going-digital/one-rom/sdrr/src/rp235x.c

// One ROM RP235X Specific Routines

// Copyright (C) 2026 Piers Finlayson <piers@piers.rocks>
//
// MIT License

#define RP235X_INCLUDES
#include "include.h"

#if defined(RP235X)

#include "roms.h"

#if defined(RP2350A) && defined(RP2350B)
#error "Cannot define both RP2350A and RP2350B"
#elif !defined(RP2350A) && !defined(RP2350B)
#error "Must define either RP2350A or RP2350B" 
#endif // RP2350A && RP2350B

// Internal function prototypes
uint8_t calculate_pll_settings(
    rp235x_clock_config_t *clock_config,
    uint8_t overclock
);
void get_clock_config(rp235x_clock_config_t *config);
uint8_t get_vreg_from_target_mhz(uint16_t target_mhz);
void setup_xosc(void);
void setup_pll(rp235x_clock_config_t *config);
void setup_usb_pll(void);
void setup_qmi(rp235x_clock_config_t *config);
void setup_vreg(rp235x_clock_config_t *config);
void setup_adc(void);
void setup_cp(void);
void final_checks(rp235x_clock_config_t *config);
uint16_t get_temp(void);

// RP2350 firmware needs a special boot block so the bootloader will load it.
// See datasheet S5.9.5 and ../include/reg-rp235x.h.
// It must be in the first 4KB of the flash firmware image.  This follows our
// reset vectors, which is fine.  Given we do not include a VECTOR_TABLE
// block, the bootloader assumes it is present at the start of flash - which it
// is.
#if !defined(TEST_BUILD)
__attribute__((section(".rp2350_block")))
#endif // !TEST_BUILD
const rp2350_boot_block_t rp2350_arm_boot_block = {
    .start_marker    = 0xffffded3,
    .image_type_tag  = 0x42,
    .image_type_len  = 0x1,
    .image_type_data = 0b0001000000100001,
    .type            = 0xff,
    .size            = 0x0001,
    .pad             = 0,
    .next_block      = 0,
    .end_marker      = 0xab123579
};

#if !defined(TEST_BUILD)

void platform_specific_init(void) {
    // RP235X needs to reset the JTAG interface to enable SWD (for example for
    // RTT logging)
    RESET_RESET |= RESET_JTAG;
    RESET_RESET &= ~RESET_JTAG;
    while (!(RESET_DONE & RESET_JTAG));
    DEBUG("JTAG reset complete");
}

// Set up interrupt to fire when VBUS sensed on PA9
void setup_vbus_interrupt(void) {
    // Check we have the information required to enable DFU
    if ((sdrr_info.extra->usb_port != PORT_0) ||
        (sdrr_info.extra->vbus_pin >= MAX_USED_GPIOS)) {
        ERR("Invalid USB port or pin for VBUS detect - not enabling USB DFU");
        return;
    }
    uint8_t vbus_pin = sdrr_info.extra->vbus_pin;

    // Enable VBUS detect interrupt
    GPIO_CTRL(vbus_pin) = GPIO_CTRL_RESET;      // Enable SIO
    uint32_t reg_offset = vbus_pin / 8;         // Which INTEx register (0-3)
    uint32_t bit = ((vbus_pin % 8) * 4) + 3;    // Bit within that register
    volatile uint32_t *inte = &IO_BANK0_PROC0_INTE0 + reg_offset;
    volatile uint32_t *intr = &IO_BANK0_INTR0 + reg_offset;
    *inte |= (1 << bit);                        // Enable rising edge interrupt
    *intr = (1 << bit);                         // Clear any pending
    NVIC_ISER0 |= (1 << IO_IRQ_BANK0);          // Enable IO_BANK0 interrupt in NVIC

    // Set as input, pull-down, output disable
    GPIO_PAD(vbus_pin) |= (PAD_PD | PAD_OUTPUT_DISABLE | PAD_INPUT);

    // Wait for pull-down to settle.  Using same delay as STM32 implementation.
    for (volatile int ii = 0; ii < 1000; ii++);

    // Check if VBUS already present
    if (GPIO_READ(vbus_pin)) {
        LOG("VBUS already present - entering bootloader");
        for (volatile int ii = 0; ii < 1000000; ii++);
        enter_bootloader();
    }
}

// VBUS interrupt Handler
void vbus_connect_handler(void) {
    // Clear the interrupt
    uint8_t vbus_pin = sdrr_info.extra->vbus_pin;
    uint32_t reg_offset = vbus_pin / 8;
    uint32_t bit = ((vbus_pin % 8) * 4) + 3;
    volatile uint32_t *intr = &IO_BANK0_INTR0 + reg_offset;
    *intr = (1 << bit);

    // Disable interrupts before logging
    __asm volatile("cpsid i");

        // Log and pause for log to complete
    LOG("VBUS detected - entering bootloader");
    for (volatile int ii = 0; ii < 1000000; ii++);

    enter_bootloader();
}
#endif // !TEST_BUILD

uint8_t calculate_pll_settings(
    rp235x_clock_config_t *config,
    uint8_t overclock
) {
    const uint32_t XOSC_MHZ = 12;
    const uint8_t REFDIV = 1;

    (void)overclock;
    
    uint32_t target_freq_mhz = config->sys_clock_freq_mhz;

    if ((target_freq_mhz > RP235X_STOCK_CLOCK_SPEED_MHZ) && (!overclock)) {
        ERR("Requested frequency %dMHz exceeds max %dMHz - cannot calculate PLL",
            target_freq_mhz, RP235X_STOCK_CLOCK_SPEED_MHZ);
        return 0;
    }
    
    uint32_t vco_min = 750;
    uint32_t vco_max = 1600;
    
    // Try POSTDIV combinations (prefer higher PD1:PD2 ratios)
    uint32_t best_error = UINT32_MAX;
    uint8_t rc = 0;
    for (uint8_t pd2 = 1; pd2 <= 7; pd2++) {
        for (uint8_t pd1 = 1; pd1 <= 7; pd1++) {
            uint32_t divisor = pd1 * pd2;
            uint32_t vco_mhz = target_freq_mhz * divisor;
            
            uint32_t fbdiv = (vco_mhz + 6) / XOSC_MHZ;  // Round to nearest
            
            if (fbdiv >= 16 && fbdiv <= 320) {
                uint32_t actual_vco = XOSC_MHZ * fbdiv;
                if (actual_vco >= vco_min && actual_vco <= vco_max) {
                    uint32_t target_vco = target_freq_mhz * divisor;
                    uint32_t error = (actual_vco > target_vco) ? 
                                    (actual_vco - target_vco) : 
                                    (target_vco - actual_vco);
                                    
                    if (error < best_error) {
                        best_error = error;
                        config->pll_refdiv = REFDIV;
                        config->pll_sys_fbdiv = (uint16_t)fbdiv;
                        config->pll_sys_postdiv1 = pd1;
                        config->pll_sys_postdiv2 = pd2;
                        rc = 1;
                    }
                }
            }
        }
    }
    
    return rc;
}

uint8_t get_vreg_from_target_mhz(uint16_t target_mhz) {
    uint8_t vreg = FIRE_VREG_1_10V;
    
    // These are conservative values.  The RP235X accepts values up to 3.30V.
    // Higher values may be required for very high overclocks, but may also
    // damage the chip or reduce its lifespan.
    //
    // To use custom VREG settngs, use firmware overrides in the ROM config.
    if (target_mhz >= 500) {
        vreg = FIRE_VREG_1_60V;
    } else if (target_mhz >= 450) {
        vreg = FIRE_VREG_1_50V;
    } else if (target_mhz >= 425) {
        vreg = FIRE_VREG_1_40V;
    } else if (target_mhz >= 400) {
        vreg = FIRE_VREG_1_30V;
    } else if (target_mhz >= 375) {
        vreg = FIRE_VREG_1_25V;
    } else if (target_mhz >= 340) {
        vreg = FIRE_VREG_1_20V;
    } else if (target_mhz > 300) {
        vreg = FIRE_VREG_1_15V;
    }

    return vreg;
}

// Figures out the PLL and VREG configuration based on the combination of
// compile time info and any ROM set overrides.
void get_clock_config(rp235x_clock_config_t *config) {
    if (sdrr_runtime_info.fire_freq == FIRE_FREQ_NONE) {
        // Use compile time setting if not overridden
        config->sys_clock_freq_mhz = TARGET_FREQ_MHZ;
    } else if (sdrr_runtime_info.fire_freq == FIRE_FREQ_STOCK) {
        // Use stock speed (150MHz) if requested
        config->sys_clock_freq_mhz = RP235X_STOCK_CLOCK_SPEED_MHZ;
    } else if (sdrr_runtime_info.fire_freq < RP235X_MAX_CONFIGURABLE_MHZ) {
        config->sys_clock_freq_mhz = sdrr_runtime_info.fire_freq;
    } else {
        ERR("Freq too high %d/%dMHz - using default", sdrr_runtime_info.fire_freq, RP235X_MAX_CONFIGURABLE_MHZ);
        config->sys_clock_freq_mhz = RP235X_STOCK_CLOCK_SPEED_MHZ;
    }

    // Check for overclocking enabled
    if (config->sys_clock_freq_mhz > RP235X_STOCK_CLOCK_SPEED_MHZ) {
        if (sdrr_runtime_info.overclock_enabled) {
            LOG("OC - %dMHz", config->sys_clock_freq_mhz);
        } else {
            ERR("No OC - cap %dMHz", RP235X_STOCK_CLOCK_SPEED_MHZ);
            config->sys_clock_freq_mhz = RP235X_STOCK_CLOCK_SPEED_MHZ;
        }
    }

    // Calculate PLL settings, to get as close to target frequency as possible.
    // This can fail for very low and very high frequencies.
    if (!calculate_pll_settings(
        config,
        sdrr_runtime_info.overclock_enabled
    )) {
        ERR("No valid PLL - using CT %dMHz", TARGET_FREQ_MHZ);
        config->sys_clock_freq_mhz = TARGET_FREQ_MHZ;  
        config->pll_refdiv = PLL_SYS_REFDIV;
        config->pll_sys_fbdiv = PLL_SYS_FBDIV;
        config->pll_sys_postdiv1 = PLL_SYS_POSTDIV1;
        config->pll_sys_postdiv2 = PLL_SYS_POSTDIV2;
    }

    // Set VREG
    if ((sdrr_runtime_info.fire_vreg != FIRE_VREG_STOCK) && (sdrr_runtime_info.fire_vreg != FIRE_VREG_NONE)) {
        // Overriding VREG
        config->vreg = sdrr_runtime_info.fire_vreg;
    } else {
        // Using calculated VREG
        config->vreg = get_vreg_from_target_mhz(config->sys_clock_freq_mhz);
    }

    DEBUG("Clock to %dMHz: refdiv=%d, fbdiv=%d, postdiv1=%d, postdiv2=%d, vreg=%d",
        config->sys_clock_freq_mhz,
        config->pll_refdiv,
        config->pll_sys_fbdiv,
        config->pll_sys_postdiv1,
        config->pll_sys_postdiv2,
        config->vreg
    );

    sdrr_runtime_info.sysclk_mhz = config->sys_clock_freq_mhz;
}

void setup_clock(void) {
    rp235x_clock_config_t config;
    get_clock_config(&config);

    setup_xosc();
    setup_qmi(&config);
    setup_vreg(&config);
    setup_pll(&config);
    setup_cp();
    final_checks(&config);
}

#if !defined(TEST_BUILD)
void setup_gpio(void) {
    // Take IO bank and pads bank out of reset
    RESET_RESET &= ~(RESET_IOBANK0 | RESET_PADS_BANK0);
    while (!(RESET_DONE & (RESET_IOBANK0 | RESET_PADS_BANK0)));

    // Set all GPIO pins to SIOs, inputs, output disable, no pulls
    for (int ii = 0; ii < MAX_USED_GPIOS; ii++) {
        GPIO_CTRL(ii) = GPIO_CTRL_RESET;
        GPIO_PAD(ii) = PAD_INPUT | PAD_OUTPUT_DISABLE;
    }

    // Go through the data pins, disabling the output disable and setting the
    // drive strength.  We don't actually set as an output here.
    // Set the drive strength to 8mA and slew rate to fast.
    const uint8_t *data_pins[] = {sdrr_info.pins->data, sdrr_info.pins->data2};
    for (int jj = 0; jj < 2; jj++) {
        for (int ii = 0; ii < 8; ii++) {
            uint8_t pin = data_pins[jj][ii];
            if (pin < MAX_USED_GPIOS) {
                GPIO_PAD(pin) &= ~PAD_OUTPUT_DISABLE;
                GPIO_PAD(pin) |= PAD_DRIVE(PAD_DRIVE_8MA) | PAD_SLEW_FAST;
                GPIO_CTRL(pin) = GPIO_CTRL_FUNC_SIO;
            } else {
                if (jj == 0) {
                    ERR("Invalid data pin %d", pin);
                }
            }
        }
    }

    // If there's a status LED, set it up as an output pin, high (LED off).
    if (sdrr_info.pins->status != INVALID_PIN) {
        uint8_t pin = sdrr_info.pins->status;
        if (pin < MAX_USED_GPIOS) {
            GPIO_PAD(pin) &= ~(PAD_OUTPUT_DISABLE | PAD_INPUT);
            GPIO_PAD(pin) |= PAD_DRIVE(PAD_DRIVE_4MA);
            SIO_GPIO_OE_SET_PIN(pin);
            SIO_GPIO_OUT_SET_PIN(pin);
        } else {
            ERR("Invalid LED %d", pin);
        }
    } else {
        DEBUG("No status LED pin defined");
    }

    // No need to set /BYTE to input - done above
}

// Reconfigure flash (QMI) speed if required
void setup_qmi(rp235x_clock_config_t *config) {
#if TARGET_FREQ_MHZ > (MAX_FLASH_CLOCK_FREQ_MHZ * 256)
#error "Flash divider > 256 not supported by the hardware"
#endif
    uint16_t target_flash_freq_mhz = config->sys_clock_freq_mhz;
    if (target_flash_freq_mhz > MAX_FLASH_CLOCK_FREQ_MHZ) {
        DEBUG("Target freq > max flash %dv%dMHz", target_flash_freq_mhz, MAX_FLASH_CLOCK_FREQ_MHZ);

        // Calculate the divider
        uint8_t divider = target_flash_freq_mhz / MAX_FLASH_CLOCK_FREQ_MHZ;
        if (target_flash_freq_mhz % MAX_FLASH_CLOCK_FREQ_MHZ) {
            divider += 1;
        }

        uint32_t m0 = XIP_QMI_M0_TIMING;
        DEBUG("Current QMI M0: 0x%08X", m0);

        m0 &= ~XIP_QMI_M0_CLKDIV_MASK;
        m0 |= (divider & XIP_QMI_M0_CLKDIV_MASK) << XIP_QMI_M0_CLKDIV_SHIFT;

        DEBUG("Update M0 clkdiv: %d", divider);
        DEBUG("Update QMI M0: 0x%08X", m0);

        XIP_QMI_M0_TIMING = m0;
    }
}

void setup_vreg(rp235x_clock_config_t *config) {
    uint32_t vreg_ctrl = POWMAN_VREG_CTRL;
    uint32_t vreg = POWMAN_VREG;
    uint8_t voltage = config->vreg;
    DEBUG("Current VREG_CTRL: 0x%08X", vreg_ctrl);
    DEBUG("Current VREG_STATUS: 0x%08X", POWMAN_VREG_STATUS);
    DEBUG("Current VREG: 0x%08X", vreg);
    DEBUG("Target VREG setting: %d", voltage);

    if (voltage > 0b11111) {
        ERR("Invalid VREG %d - ignore", voltage);
        return;
    }

    if (config->vreg != FIRE_VREG_1_10V) {
        uint8_t high_temp = HT_TH_100;
        uint8_t unlimited_voltage = 0;
        if (config->vreg > FIRE_VREG_1_30V) {
            unlimited_voltage = 1;
        }

        DEBUG("Unlock VREG");
        vreg_ctrl |= POWMAN_PASSWORD |
                POWMAN_VREG_CTRL_UNLOCK;
        POWMAN_VREG_CTRL = vreg_ctrl;
        while (!(POWMAN_VREG_CTRL & POWMAN_VREG_CTRL_UNLOCK));

        if (unlimited_voltage) {
            ERR("Disable voltage limit");
            vreg_ctrl |= POWMAN_VREG_CTRL_DISABLE_VOLTAGE_LIMIT;
            POWMAN_VREG_CTRL = vreg_ctrl;
            while (!(POWMAN_VREG_CTRL & POWMAN_VREG_CTRL_DISABLE_VOLTAGE_LIMIT));
        }

        DEBUG("Set VREG high temp %d", high_temp);
        vreg_ctrl &= ~(HT_TH_MASK << HT_TH_SHIFT);
        vreg_ctrl |= POWMAN_PASSWORD |
                        POWMAN_VREG_CTRL_HT_TH(high_temp);
        POWMAN_VREG_CTRL = vreg_ctrl;
        DEBUG("Current VREG_CTRL: 0x%08X", POWMAN_VREG_CTRL);

        DEBUG("Set VREG to %d", voltage);
        while (POWMAN_VREG & POWMAN_VREG_UPDATE);
        vreg &= ~(VREG_MASK << VREG_SHIFT);
        vreg |= POWMAN_VREG_VOLTAGE(voltage) | POWMAN_PASSWORD;
        POWMAN_VREG = vreg;
        while (POWMAN_VREG & POWMAN_VREG_UPDATE);

        DEBUG("POWMAN_VREG: 0x%08X", POWMAN_VREG);

        for (volatile int ii = 0; ii < 5000; ii++) {
            // Wait a bit for the voltage to stabilise
            // 2,000 loops is too few at 540MHz, 5,000 seems like enough
            // Probabyl not required if DEBUG logging is on
        }
    } 
}

// Set up the PLL with the generated values
void setup_pll(rp235x_clock_config_t *config) {
    // Release PLL_SYS from reset
    RESET_RESET &= ~RESET_PLL_SYS;
    while (!(RESET_DONE & RESET_PLL_SYS));

    // Power down the PLL, set the feedback divider
    PLL_SYS_PWR = PLL_PWR_PD | PLL_PWR_VCOPD;

    // Set feedback divider and reference divider
    PLL_SYS_FBDIV_INT = config->pll_sys_fbdiv;
    PLL_SYS_CS = PLL_CS_REFDIV(config->pll_refdiv);

    // Power up VCO (keep post-dividers powered down)
    PLL_SYS_PWR = PLL_PWR_POSTDIVPD;

    // Wait for PLL to lock
    while (!(PLL_SYS_CS & PLL_CS_LOCK));

    // Set post dividers and power up everything
    PLL_SYS_PRIM = PLL_PRIM_POSTDIV1(config->pll_sys_postdiv1) |
                     PLL_PRIM_POSTDIV2(config->pll_sys_postdiv2);

    // Power up post dividers
    PLL_SYS_PWR = 0;

    // Switch to the PLL
    CLOCK_SYS_CTRL = CLOCK_SYS_SRC_AUX | CLOCK_SYS_AUXSRC_PLL_SYS;
    while ((CLOCK_SYS_SELECTED & (1 << 1)) == 0);
}

void setup_usb_pll(void) {
    DEBUG("Setting up USB PLL");

    // Release PLL_USB from reset
    RESET_RESET &= ~RESET_PLL_USB;
    while (!(RESET_DONE & RESET_PLL_USB));

    // Power down the PLL, set the feedback divider
    PLL_USB_PWR = PLL_PWR_PD | PLL_PWR_VCOPD;

    // For 48MHz: 12MHz × 40 ÷ 10 ÷ 1 = 48MHz
    PLL_USB_FBDIV_INT = 40;
    PLL_USB_CS = PLL_CS_REFDIV(1);

    // Power up VCO (keep post-dividers powered down)
    PLL_USB_PWR = PLL_PWR_POSTDIVPD;

    // Wait for lock
    while (!(PLL_USB_CS & PLL_CS_LOCK));

    // Set post dividers: 40 × 12MHz = 480MHz → ÷10 ÷1 = 48MHz
    PLL_USB_PRIM = PLL_PRIM_POSTDIV1(10) | PLL_PRIM_POSTDIV2(1);

    // Power up
    PLL_USB_PWR = 0;
}

void setup_adc(void) {
    DEBUG("Setting up ADC");

    // Route USB PLL to ADC (USB is the default source so no need to set)
    CLOCK_ADC_CTRL |= CLOCK_ADC_ENABLE;
    while (!(CLOCK_ADC_CTRL & CLOCK_ADC_ENABLED));
    DEBUG("ADC clock enabled");

    // Take ADC out of reset
    RESET_RESET &= ~(RESET_ADC);
    while (!(RESET_DONE & RESET_ADC));

    // Enable ADC and temperature sensor
    DEBUG("ADC out of reset");
    ADC_CS |= ADC_CS_TS_EN | ADC_CS_EN;
    while (!(ADC_CS & ADC_CS_READY));          

    DEBUG("ADC ready");
}

uint16_t get_temp(void) {
    // Start a conversion
    ADC_CS |= ADC_CS_AINSEL(ADC_CS_TS);
    ADC_CS |= ADC_CS_START_ONCE;

    // Wait for it to complete
    while (!(ADC_CS & ADC_CS_READY));

    // Return the result
    return (uint16_t)(ADC_RESULT & ADC_RESULT_MASK);
}
#endif // !TEST_BUILD

void final_checks(rp235x_clock_config_t *config) {
    if (config->sys_clock_freq_mhz > 300) {
        DEBUG("!!!Extreme overlocking - enabling and reading temp sensor");

        // USB clock required for ADC
        setup_usb_pll();

        // Set up ADC
        setup_adc();

        // Take a reading
        uint16_t temp = get_temp();
        (void)temp;  // In case not logged

        ERR("Temperature sensor reading: 0x%03X", temp);
    }
}

#if !defined(TEST_BUILD)
void setup_cp(void) {
#if defined(RP_USE_CP)
    // Enable Coprocessor 0 to enable MCR instructions
    SCB_CPACR &= ~(0b11 << 0);
    SCB_CPACR |= SCB_CPACR_CP0_FULL;
    __asm volatile ("dsb");
    __asm volatile ("isb");
    DEBUG("CP0 enabled");
#endif // RP_USE_CP
}
#endif // !TEST_BUILD

void setup_mco(void) {
    ERR("MCO not supported on RP235X");
}

#if !defined(TEST_BUILD)
// Set up the image select pins to be inputs with the appropriate pulls.
//
// As of 0.6.0 sel_jumper_pulls is a bit field indicating whether the
// jumper pulls up (1) or down (0) each sel pin individually.
//
// As of 0.6.2 moved to uint64_t to cope with RP2350B.
uint32_t setup_sel_pins(uint64_t *sel_mask, uint64_t *flip_bits) {
    uint32_t num;
    uint32_t pad;

    // Initialize outputs
    *sel_mask = 0;
    *flip_bits = 0;

    num = 0;
    for (int ii = 0; (ii < MAX_IMG_SEL_PINS); ii++) {
        uint8_t pin = sdrr_info.pins->sel[ii];
        
        if (pin >= MAX_USED_GPIOS) {
            // Ignore invalid pins
            continue;
        }
        
        if ((pin == sdrr_info.pins->swclk_sel) ||
            (pin == sdrr_info.pins->swdio_sel)) {
            DEBUG("Pin %d = SWD, disable", pin);

            SYSCFG_DBGFORCE |= SYSCFG_DBGFORCE_ATTACH_BIT;
            
            if (pin == sdrr_info.pins->swclk_sel) {
                GPIO_PAD(SWCLK_PAD) = (1 << PAD_ISO_BIT);
            }
            if (pin == sdrr_info.pins->swdio_sel) {
                GPIO_PAD(SWDIO_PAD) = (1 << PAD_ISO_BIT);
            }
        }
        
        if (pin < MAX_USED_GPIOS) {
            // Set the appropriate pad value based on the bit field
            if (sdrr_info.pins->sel_jumper_pull & (1 << ii)) {
                // This pin pulls up, so we pull down
                DEBUG("Pin %d PD", pin);
                pad = PAD_INPUT_PD;
            } else {
                // This pin pulls down, so we pull up
                DEBUG("Pin %d PU", pin);
                pad = PAD_INPUT_PU;

                // Flip this bit when reading the SEL pins, as closing will
                // pull the pin low, but that should read a
                *flip_bits |= (1ULL << pin);
            }

            // Enable pull
            GPIO_PAD(pin) = pad;

            // Set the pin in our bit mask
            *sel_mask |= (1ULL << pin);

            num += 1;
        } else if (pin != INVALID_PIN) {
            ERR("Pin %d >= %d - ignore", pin, MAX_USED_GPIOS);
        }
    }

    // Short delay to allow the pulls to settle.
    for(volatile int ii = 0; ii < 10; ii++);

    return num;
}

// Get the value of the sel pins.
// 
// As of 0.6.0, we support sel_jumper_pulls as a bit field indicating whether
// each individual sel pin's jumper pulls up (1) or down (0).
//
// If a pull is low (i.e. closing the jumpers pulls them up) we return the
// value as is, as closed should indicate 1.  In the other case, where MCU
// pulls are high (closing jumpers) pulls the pins low, we invert - so closed
// still indicates 1.
uint64_t get_sel_value(uint64_t sel_mask, uint64_t flip_bits) {
    uint64_t gpio_value = 0;

    // Read GPIO input register.  We read multiple times to allow for any
    // spurious "highs", as some pins that the sel pin connected to might
    // ocassionally glitch high.  A case in point is BOOT, which is shared
    // with QSPI_SS.  This will mostly be low, as it is the main external
    // flash chip select, and seems to always read low, but could go high
    // if, for some reason, flash isn't busy.
    //
    // The logic below is as it is because in this case the spurious high
    // ends up being a spuripous low after flipping (cos closing that jumper
    // pulls the pin low).
    //
    // This isn't totally robust.  Scoping One ROM during this stage shows
    // that QSPI_SS is almost always low, but it does glitch high every 40us,
    // for perhaps 100ns, so there is a change of misreading.  If this turns
    // out to be a problem, we should run this from RAM, disable XIP and
    // isolate the QSPI_SS pad (like we do SWD pads).  Or, force some explicit
    // flash reads, or even just take more votes.  I'm hoping that's not
    // necessary.

    // Take 10-20 samples spread over ~1us to avoid any single glitch.
    // At 150MHz, this is negligible cost (<150 cycles total).
    for (int i = 0; i < 15; i++) {
        uint32_t low_gpios = SIO_GPIO_IN;
        uint32_t high_gpios = SIO_GPIO_HI_IN;
        uint64_t gpios = ((uint64_t)high_gpios << 32) | low_gpios;
        gpio_value |= (gpios ^ flip_bits);
    }

    // Mask to just the sel pins
    gpio_value &= sel_mask;

    return gpio_value;
}

void disable_sel_pins(void) {
    for (int ii = 0; (ii < MAX_IMG_SEL_PINS); ii++) {
        uint8_t pin = sdrr_info.pins->sel[ii];
        if (pin < MAX_USED_GPIOS) {
            // Disable pulls
            GPIO_PAD(pin) = ~(PAD_PU | PAD_PD);

            SYSCFG_DBGFORCE &= ~SYSCFG_DBGFORCE_ATTACH_BIT;

            if ((pin == sdrr_info.pins->swclk_sel) ||
                (pin == sdrr_info.pins->swdio_sel)) {
                DEBUG("Restore pin %d", pin);

                // Use measured value to restore function
                if (pin == sdrr_info.pins->swclk_sel) {
                    GPIO_PAD(SWCLK_PAD) = 0x5A;
                } else {
                    GPIO_PAD(SWDIO_PAD) = 0x5A;
                }
            }
        }
    }
}
#endif // !TEST_BUILD

void setup_status_led(void) {
    // No-op - done in setup_gpio()
}

void blink_pattern(uint32_t on_time, uint32_t off_time, uint8_t repeats) {
    if (sdrr_info.status_led_enabled && sdrr_info.pins->status_port == PORT_0 && sdrr_info.pins->status <= MAX_USED_GPIOS) {
        uint8_t pin = sdrr_info.pins->status;
        for(uint8_t i = 0; i < repeats; i++) {
            status_led_on(pin);
            delay(on_time);
            status_led_off(pin);
            delay(off_time);
        }   
    }
}

#if !defined(TEST_BUILD)
// Enters bootloader mode.
void enter_bootloader(void) {
    // Look up the reboot function from ROM
    typedef int (*reboot_fn_t)(uint32_t flags, uint32_t delay_ms, uint32_t p0, uint32_t p1);
    typedef void *(*rom_table_lookup_fn)(uint32_t code, uint32_t mask);
    
#pragma GCC diagnostic push
#pragma GCC diagnostic ignored "-Warray-bounds"
    rom_table_lookup_fn rom_table_lookup = 
        (rom_table_lookup_fn)(uintptr_t)*(uint16_t*)(0x00000016);
#pragma GCC diagnostic pop
    
    // 0x0004 is ARM secure mode
    uint32_t reboot_code = ('B' << 8) | 'R';
    reboot_fn_t reboot = (reboot_fn_t)rom_table_lookup(reboot_code, 0x0004);

    if (reboot == NULL) {
        ERR("Unable to find reboot function in ROM - cannot enter bootloader");
        return;
    }

    // Reboot into BOOTSEL mode with status LED as activity indicator (active low)
    uint32_t flags = 0x0100 | 0x0002;   // No return on success | BOOTSEL mode
    uint32_t ms_delay = 10; // 10ms delay before reboot, needs to be non-zero
    uint32_t p0 = 0;
    uint32_t p1 = 0;

    // There is a bug in the Pico SDK and RP2350 datasheet defining p0 and p1
    // for reboot() when using REBOOT_TYPE_BOOTSEL (0x0002).  p0 and p1 have
    // been transposed.  p1 is the status LED pin, p0 the flags.  We don't want
    // to enable the status LED, because it looks too much like One ROM is
    // ready to serve bytes.  Hence we leave it disabled.  This makes it light
    // up dimly, just like during initial power-on.
    // 
    // However, we do want to explicitly disable mass storage mode, so we set
    // bit 0 of p0 (not p1!).  If you want mass storage mode, jump BOOTSEL to
    // GND when plugging in.
    p0 |= 0x01;     // Disable mass storage mode
    reboot(flags, ms_delay, p0, p1);
}
#endif // !TEST_BUILD

void check_config(
    const sdrr_info_t *info,
    sdrr_runtime_info_t *runtime,
    const sdrr_rom_set_t *set
) {
    uint8_t failed = 0;
    const uint8_t chip_pins = info->pins->chip_pins;
    if ((chip_pins != 24) && (chip_pins != 28) && (chip_pins != 32) && (chip_pins != 40)) {
        ERR("Invalid ROM pins: %d", chip_pins);
        failed = 1;
    } else if (chip_pins >= 28) {
        if (runtime->fire_serve_mode == FIRE_SERVE_CPU) {
            ERR("ROM requires PIO support");
            failed = 1;
        }
    }

    // Check ports (banks on RP235X) are as expected
    if (info->pins->data_port != PORT_0) {
        ERR("Data pins should be using bank 0");
        failed = 1;
    }
    if (info->pins->addr_port != PORT_0) {
        ERR("Address pins should be using bank 0");
        failed = 1;
    }
    if (info->pins->cs_port != PORT_0) {
        ERR("CS pins should be using bank 0");
        failed = 1;
    }
    if (info->pins->sel_port != PORT_0) {
        ERR("Sel pins should be using bank 0");
        failed = 1;
    }

    // Count the number of data pins
    uint8_t data_pins = 0;
    for (int ii = 0; ii < 8; ii++) {
        if (info->pins->data[ii] < MAX_USED_GPIOS) {
            data_pins += 1;
        }
    }
    for (int ii = 0; ii < 8; ii++) {
        if (info->pins->data2[ii] < MAX_USED_GPIOS) {
            data_pins += 1;
        }
    }
    runtime->num_data_pins = data_pins;

    if (chip_pins == 24) {
        if (runtime->fire_serve_mode == FIRE_SERVE_CPU) {
            // Checks on valid for CPU serving mode

            // We expect to use pins 0-15 or 8-23 for address lines
            uint8_t seen_a_0_7 = 0;
            uint8_t seen_a_16_23 = 0;
            for (int ii = 0; ii < 13; ii++) {
                uint8_t pin = info->pins->addr[ii];
                if (pin < 8) {
                    seen_a_0_7 = 1;
                } else if (pin > 15) {
                    seen_a_16_23 = 1;
                }
            }
            if (seen_a_0_7 && seen_a_16_23) {
                ERR("ROM address lines using invalid mix of pins");
                failed = 1;
            }

            // We expect to use pins 0-7 or 16-23 for data lines
            uint8_t seen_d_0_7 = 0;
            uint8_t seen_d_16_23 = 0;
            for (int ii = 0; ii < 8; ii++) {
                uint8_t pin = info->pins->data[ii];
                if (pin < 8) {
                    seen_d_0_7 = 1;
                } else if (pin > 15) {
                    seen_d_16_23 = 1;
                }
            }
            if (seen_d_0_7 && seen_d_16_23) {
                ERR("ROM data lines using invalid mix of pins");
                failed = 1;
            }

            // Check X1/X2 pins
            if (set->rom_count > 1) {
                if (seen_a_0_7 && (info->pins->x1 > 16)) {
                    ERR("Multi-ROM mode, but pin X1 invalid");
                    failed = 1;
                }
                if (seen_a_0_7 && (info->pins->x2 > 17)) {
                    ERR("Multi-ROM mode, but pin X2 invalid");
                    failed = 1;
                }
                if (seen_a_16_23 && ((info->pins->x1 < 8) || (info->pins->x1 > 23))) {
                    ERR("Multi-ROM mode, but pin X1 invalid");
                    failed = 1;
                }
                if (seen_a_16_23 && ((info->pins->x2 < 8) || (info->pins->x2 > 23))) {
                    ERR("Multi-ROM mode, but pin X2 invalid");
                    failed = 1;
                }
                if (info->pins->x1 == info->pins->x2) {
                    ERR("Multi-ROM mode, but pin X1==X2");
                    failed = 1;
                }
                if (info->pins->x_jumper_pull > 1) {
                    ERR("X jumper pull value invalid");
                    failed = 1;
                }
            }
        }
    } else if (chip_pins == 28) {
        // Check CS and CE/OE lines are valid
        uint8_t ce_pin = info->pins->ce;
        uint8_t oe_pin = info->pins->oe;
        uint8_t cs1_pin = info->pins->cs1;
        uint8_t cs2_pin = info->pins->cs2;
        uint8_t cs3_pin = info->pins->cs3;
        if ((cs1_pin >= MAX_USED_GPIOS) ||
            (cs2_pin >= MAX_USED_GPIOS) ||
            (cs3_pin >= MAX_USED_GPIOS) ||
            (ce_pin >= MAX_USED_GPIOS) ||
            (oe_pin >= MAX_USED_GPIOS)) {
            ERR("28-pin requires 3xCS and CE/OE");
            failed = 1;
        }

        // Check that we have 18 address pins (16 in addr, 2 in addr2).  Also,
        // check CE/OE lines are within the address lines.
        uint8_t ce_in_addr = 0;
        uint8_t oe_in_addr = 0;
        uint8_t num_addr_pins = 0;
        for (int ii = 0; ii < 16; ii++) {
            if (info->pins->addr[ii] < MAX_USED_GPIOS) {
                num_addr_pins += 1;
                if (info->pins->addr[ii] == ce_pin) {
                    ce_in_addr = 1;
                }
                if (info->pins->addr[ii] == oe_pin) {
                    oe_in_addr = 1;
                }
            }
        }
        for (int ii = 0; ii < 2; ii++) {
            if (info->pins->addr2[ii] < MAX_USED_GPIOS) {
                num_addr_pins += 1;
            }
            if (info->pins->addr2[ii] == ce_pin) {
                ce_in_addr = 1;
            }
            if (info->pins->addr2[ii] == oe_pin) {
                oe_in_addr = 1;
            }
        }
        if (num_addr_pins != 18) {
            ERR("28-pin requires 18 addr pins");
            failed = 1;
        }
        if (!ce_in_addr || !oe_in_addr) {
            ERR("28-pin requires CE/OE within addr pins");
            failed = 1;
        }

        // Check that image size is either 64KB or 256KB
        uint32_t img_size = set->size;
        if ((img_size != 64 * 1024) && (img_size != 256 * 1024)) {
            ERR("28-pin ROM image incorrect size 0x%08X", img_size);
            failed = 1;
        }

        // Other checking we could do includes that all CS/CE/OE and address
        // pins are contiguous
    } else if (chip_pins == 32) {
        // Check CS and CE/OE lines are valid
        uint8_t ce_pin = info->pins->ce;
        uint8_t oe_pin = info->pins->oe;
        uint8_t cs1_pin = info->pins->cs1;  // 27C080 A19
        uint8_t cs2_pin = info->pins->cs2;  // 27C301 /OE
        if ((cs1_pin >= MAX_USED_GPIOS) ||
            (cs2_pin >= MAX_USED_GPIOS) ||
            (ce_pin >= MAX_USED_GPIOS) ||
            (oe_pin >= MAX_USED_GPIOS)) {
            ERR("32-pin requires 2xCS and CE/OE");
            failed = 1;
        }

        // Check that we have 19 address pins (16 in addr, 3 in addr2)
        uint8_t num_addr_pins = 0;
        for (int ii = 0; ii < 16; ii++) {
            if (info->pins->addr[ii] < MAX_USED_GPIOS) {
                num_addr_pins += 1;
            }
        }
        for (int ii = 0; ii < 3; ii++) {
            if (info->pins->addr2[ii] < MAX_USED_GPIOS) {
                num_addr_pins += 1;
            }
        }
        if (num_addr_pins != 19) {
            ERR("32-pin requires 19 addr pins");
            failed = 1;
        }

        // Check that image size is 512KB
        uint32_t img_size = set->size;
        if (img_size != 512 * 1024) {
            ERR("32-pin ROM image incorrect size 0x%08X", img_size);
            failed = 1;
        }

        // Other checking we could do includes that all CS/CE/OE and address
        // pins are contiguous
    } else if (chip_pins == 40) {
        // Check that we have 19 address pins (16 in addr, 3 in addr2)
        uint8_t num_addr_pins = 0;
        for (int ii = 0; ii < 16; ii++) {
            if (info->pins->addr[ii] < MAX_USED_GPIOS) {
                num_addr_pins += 1;
            }
        }
        for (int ii = 0; ii < 3; ii++) {
            if (info->pins->addr2[ii] < MAX_USED_GPIOS) {
                num_addr_pins += 1;
            }
        }
        if (num_addr_pins != 19) {
            ERR("40-pin requires 19 addr pins");
            failed = 1;
        }

        // Check we have 16 data pins
        if (runtime->num_data_pins < 16) {
            ERR("40 pin requires 16 data pins");
            failed = 1;
        }

        // Check we have a byte pin
        uint8_t byte_pin = info->pins->byte;
        if (byte_pin >= MAX_USED_GPIOS) {
            ERR("40-pin requires BYTE pin");
            failed = 1;
        }

        // Other checking we do do includes CE/OE not being in address pins
    } else {
        ERR("Unsupported chip pins: %d", chip_pins);
        failed = 1;
    }

    // As of 0.6.0 sel_jumper_pulls is a bit field.  Check it isn't larger
    // than it should be given the number of valid sel pins.
    uint8_t sel_pins_used = 0;
    for (int ii = 0; ii < MAX_IMG_SEL_PINS; ii++)
    {
        if (info->pins->sel[ii] < MAX_USED_GPIOS) {
            sel_pins_used += 1;
        }
    }
    if (info->pins->sel_jumper_pull >= (1 << sel_pins_used)) {
        ERR("Sel jumper pull value invalid for number of sel pins used");
        failed = 1;
    }

    // Warn if serve mode is incorrectly set for multiple ROM images
    if ((set->rom_count == 1) && (set->serve == SERVE_ADDR_ON_ANY_CS)) {
        // Correction is done in main_loop() using a local variable
        ERR("Single ROM image - wrong serve mode - will correct");
    }

    if (failed) {
        ERR("Invalid configuration - entering limp mode");
        limp_mode(LIMP_MODE_INVALID_CONFIG);
    }
}

#if !defined(TEST_BUILD)
void platform_logging(void) {
#if defined(BOOT_LOGGING)
    // Reset the SysInfo registers
    RESET_RESET &= ~RESET_SYSINFO;

#if defined(RP2350A) 
    if (SYSINFO_IS_QFN60()) {
        LOG("%s RP2350A", sdrr_info.hw_rev);
#if defined(DEBUG_LOGGING)
#endif // DEBUG_LOGGING
    } else {
        ERR("%s RP2350B but built for RP2350A", sdrr_info.hw_rev);
        limp_mode(LIMP_MODE_INVALID_BUILD);
    }
#elif defined(RP2350B)
    if (!SYSINFO_IS_QFN60()) {
        LOG("%s RP2350B", sdrr_info.hw_rev);
    } else {
        ERR("%s RP2350A but built for RP2350B", sdrr_info.hw_rev);
        limp_mode(LIMP_MODE_INVALID_BUILD);
    }
#else 
#error "MCU variant not specified"
#endif
    DEBUG("Chip ID: 0x%08X", SYSINFO_CHIP_ID);
    DEBUG("Chip commit: 0x%08X", SYSINFO_GITREF_RP2350);
    DEBUG("Core: %d", SIO_CPUID);
    if ((MCU_RAM_SIZE_KB != RP2350_RAM_SIZE_KB) || (MCU_RAM_SIZE != (RP2350_RAM_SIZE_KB * 1024))) {
        ERR("RAM error: actual %dKB, expected: %dKB",
            MCU_RAM_SIZE_KB,
            RP2350_RAM_SIZE_KB);
        limp_mode(LIMP_MODE_INVALID_BUILD);
    } else {
        LOG("RAM: %dKB", MCU_RAM_SIZE_KB);
    }
    LOG("Flash: %dKB", MCU_FLASH_SIZE_KB);
    LOG("Freq: %dMHz", TARGET_FREQ_MHZ);
    LOG("PLL: %d/%d/%d/%d", PLL_SYS_REFDIV, PLL_SYS_FBDIV, PLL_SYS_POSTDIV1, PLL_SYS_POSTDIV2);

#endif // BOOT_LOGGING
}

void setup_xosc(void) {
    // Initialize XOSC peripheral.  We are using the 12MHz xtal from the
    // reference hardware design, so we can use values from the datasheet.
    // See S8.2 for more details.
    //
    // Specifically:
    // - Set the startup delay to 1ms
    // - Enable the XOSC giving it the appropriate frequency range (1-15MHz)
    // - Wait for the XOSC to be enabled and stable
    XOSC_STARTUP = 47;
    XOSC_CTRL = XOSC_ENABLE | XOSC_RANGE_1_15MHz;
    while (!(XOSC_STATUS & XOSC_STATUS_STABLE));
    DEBUG("XOSC enabled");

    // Switch CLK_REF to use XOSC instead of the ROSC
    CLOCK_REF_CTRL = CLOCK_REF_SRC_XOSC;
    while ((CLOCK_REF_SELECTED & CLOCK_REF_SRC_SEL_XOSC) != CLOCK_REF_SRC_SEL_XOSC);
}
#endif // !TEST_BUILD

#endif // RP235X
