going-digital/one-rom/sdrr/include/piodma/piodma.h

// Copyright (C) 2026 Piers Finlayson <piers@piers.rocks>
//
// MIT License

#ifndef PIODMA_H
#define PIODMA_H

#if defined(DEBUG_LOGGING)
#define APIO_LOG_ENABLE DEBUG
#endif // DEBUG_LOGGING

#include <apio.h>
#include "piodma/dmareg.h"

#endif // PIODMA_H
