going-digital/one-rom/sdrr/src/vector.c

// One ROM - Vector table and reset handler.

// Copyright (C) 2025 Piers Finlayson <piers@piers.rocks>
//
// MIT License

#if !defined(TEST_BUILD)

#include "include.h"

// Forward declarations
void Reset_Handler(void);
void Default_Handler(void);
void NMI_Handler(void);
void HardFault_Handler(void);
void BusFault_Handler(void);
void UsageFault_Handler(void);

// Default exception/interrupt handlers
#define MemManage_Handler   Default_Handler
#define SVC_Handler         Default_Handler
#define DebugMon_Handler    Default_Handler
#define PendSV_Handler      Default_Handler
#define SysTick_Handler     Default_Handler

// Declare stack section
extern uint32_t _estack;

// Vector table - must be placed at the start of flash
__attribute__ ((section(".isr_vector"), used))
void (* const g_pfnVectors[])(void) = {
    (void (*)(void))&_estack,      // Initial stack pointer
    Reset_Handler,                 // Reset handler
    NMI_Handler,                   // NMI handler
    HardFault_Handler,             // Hard fault handler
    MemManage_Handler,             // MPU fault handler
    BusFault_Handler,              // Bus fault handler
    UsageFault_Handler,            // Usage fault handler
    0, 0, 0, 0,                    // Reserved
    SVC_Handler,                   // SVCall handler
    DebugMon_Handler,              // Debug monitor handler
    0,                             // Reserved
    PendSV_Handler,                // PendSV handler
    SysTick_Handler,               // SysTick handler

    // Peripheral interrupt handlers follow 0-15 above.
    // 16-19
    Default_Handler, Default_Handler, Default_Handler, Default_Handler,
    // 20-23
    Default_Handler, Default_Handler, Default_Handler, Default_Handler,
    // 24-27
    Default_Handler, Default_Handler, Default_Handler, Default_Handler,
    // 28-31
    Default_Handler, Default_Handler, Default_Handler, Default_Handler,
    // 32-35
    Default_Handler, Default_Handler, Default_Handler, Default_Handler,
    // 36-39
#if defined(STM32F4)
    Default_Handler, Default_Handler, Default_Handler, vbus_connect_handler,
#else // RP235X
    Default_Handler, vbus_connect_handler, Default_Handler, Default_Handler,
#endif 
    // 40-43
    Default_Handler, Default_Handler, Default_Handler, Default_Handler,
    Default_Handler, Default_Handler, Default_Handler, Default_Handler,
    Default_Handler, Default_Handler, Default_Handler, Default_Handler,
    Default_Handler, Default_Handler, Default_Handler, Default_Handler,
    Default_Handler, Default_Handler, Default_Handler, Default_Handler,
    Default_Handler, Default_Handler, Default_Handler, Default_Handler,
    Default_Handler, Default_Handler, Default_Handler, Default_Handler,
    Default_Handler, Default_Handler, Default_Handler, Default_Handler,
    Default_Handler, Default_Handler, Default_Handler, Default_Handler,
    Default_Handler, Default_Handler, Default_Handler, Default_Handler,
    Default_Handler, Default_Handler, Default_Handler, Default_Handler,
    Default_Handler, Default_Handler, Default_Handler, Default_Handler,
    Default_Handler, Default_Handler, Default_Handler, Default_Handler,
    Default_Handler, Default_Handler, Default_Handler, Default_Handler,
    Default_Handler, Default_Handler, Default_Handler, Default_Handler,
    Default_Handler, Default_Handler, Default_Handler, Default_Handler,
    Default_Handler, Default_Handler, Default_Handler, Default_Handler,
    Default_Handler, Default_Handler, Default_Handler, Default_Handler,
    // Different STM32F4s have different numbers of interrupts.  The maximum
    // appears to be 96 (F446), which is what's included here.  This means
    // that 0x080001C4 onwards is free, but we'll not use anything until
    // 0x08000200 to be safe.
    // Note that the RP2350 has 52, so this is sufficient.  See datasheet
    // S3.2 - Interrupts
};

//
// Variables defined by the linker.
//
// Note these are "labels" that mark memory addresses, not variables that
// store data.  The address of the label IS the address we're interested in.
// Hence we use & below to get the addresses that these labels represent.
extern uint32_t _sidata;    // Start of .data section in FLASH
extern uint32_t _sdata;     // Start of .data section in RAM
extern uint32_t _edata;     // End of .data section in RAM
extern uint32_t _sbss;      // Start of .bss section in RAM
extern uint32_t _ebss;      // End of .bss section in RAM

// Location of RAM reserved for executing the main loop function from, if
// EXECUTE_FROM_RAM is defined.
#if defined(EXECUTE_FROM_RAM)
extern uint32_t _main_loop_start;   // Start of .main_loop section in FLASH
extern uint32_t _main_loop_end;     // End of .main_loop section in FLASH
extern uint32_t _ram_func_start;    // Start of .ram_func section in RAM
extern uint32_t _ram_func_end;      // End of .ram_func section in RAM
#endif

extern uint32_t _sdrr_runtime_info_ram[]; // Start of .sdrr_runtime_info section in RAM
extern uint32_t _sdrr_runtime_info_flash[];   // Start of .sdrr_runtime_info section in flash
extern uint32_t _sdrr_runtime_info_end[];   // End of .sdrr_runtime_info section in flash

// Reset handler
void Reset_Handler(void) {
    // Enable hard floating point support:
    // - Same on STM32F4 M4 and RP235X Cortex-M33
    // - Enable CP10 and CP11 (FP extension) in the Cortex-M33
    SCB_CPACR |= (0xF << 20); // Enable CP10 and CP11 full access
    __asm volatile ("dsb");
    __asm volatile ("isb");

    // Check if we need to enter STM32 DFU (bootloader) mode
#ifdef STM32F4
    if (sdrr_runtime_info.bootloader_entry == ENTER_BOOTLOADER_MAGIC) {
        // Clear the magic value to avoid re-entering bootloader on next reset
        sdrr_runtime_info.bootloader_entry = 0;

        // Enter bootloader
        dfu();
    }
#endif

    // We use memcpy and memset because it's likely to be faster than anything
    // we could come up with.

    // Copy sdrr_runtime_info_t from flash to RAM
    memcpy(_sdrr_runtime_info_ram,
        _sdrr_runtime_info_flash,
           (unsigned int)((char*)_sdrr_runtime_info_end - (char*)_sdrr_runtime_info_ram));
    sdrr_runtime_info_t *runtime_info = (sdrr_runtime_info_t *)_sdrr_runtime_info_ram;
    runtime_info->status_led_enabled = sdrr_info.status_led_enabled;
    runtime_info->swd_enabled = sdrr_info.swd_enabled;

    // Copy data section from flash to RAM
    memcpy(&_sdata, &_sidata, (unsigned int)((char*)&_edata - (char*)&_sdata));
    
    // Zero out bss section  
    memset(&_sbss, 0, (unsigned int)((char*)&_ebss - (char*)&_sbss));
    
#if defined(EXECUTE_FROM_RAM)
    // Copy main_loop function into RAM.
    uint32_t code_size = (unsigned int)((char*)&_main_loop_end - (char*)&_main_loop_start);
#if defined(BOOT_LOGGING)
    if (code_size > (unsigned int)((char*)&_ram_func_end - (char*)&_ram_func_start)) {
        ERR("Code size too large for RAM function area");
    }
#endif // BOOT_LOGGING
    copy_func_to_ram((void (*)(void))(&_main_loop_start), (uint32_t)&_ram_func_start, code_size);
#endif // EXECUTE_FROM_RAM

    // Call the main function
    main();
    
    // In case main returns
    while(1);
}

// Default handler for unhandled interrupts - fast continuous blink
void Default_Handler(void) {
    // Use sdrr_info status_led_enabled in case runtime_info is
    // corrupted/not initialized.  Note this overrides any LED override
    if (sdrr_info.status_led_enabled) {
        setup_status_led();
        while (1) {
            blink_pattern(100000, 100000, 255);
        }
    }
}

// NMI_Handler - single blink pattern
void NMI_Handler(void) {
    setup_status_led();
    
    while(1) {
        blink_pattern(100000, 500000, 1); // Single blink
        delay(1000000); // Long pause
    }
}

// HardFault_Handler - double blink pattern
void HardFault_Handler(void) {
    setup_status_led();
    
    while(1) {
        blink_pattern(100000, 200000, 2); // Double blink
        delay(1000000); // Long pause
    }
}

// BusFault_Handler - triple blink pattern
void BusFault_Handler(void) {
    setup_status_led();
    
    while(1) {
        blink_pattern(100000, 200000, 3); // Triple blink
        delay(1000000); // Long pause
    }
}

// UsageFault_Handler - quadruple blink pattern
void UsageFault_Handler(void) {
    setup_status_led();
    
    while(1) {
        blink_pattern(100000, 200000, 4); // Quadruple blink
        delay(1000000); // Long pause
    }
}

#endif // !TEST_BUILD
