going-digital/one-rom/sdrr/include/constants.h

// Contains constants

// Copyright (C) 2025 Piers Finlayson <piers@piers.rocks>
//
// MIT License

#ifndef CONSTANTS_H
#define CONSTANTS_H

// Metadata strings to include in the binary
extern const char mcu_variant[];
extern const char license[];
extern const char project_url[];
extern const char copyright[];
extern const char author[];
extern const char product[];
extern const char rom_type[];
extern const char log_divider[];
extern const char inverted[];
extern const char r2364[];
extern const char r2332[];
extern const char r2316[];
extern const char unknown[];
extern const char cs_low[];
extern const char cs_high[];
extern const char cs_na[];
extern const char flash[];
extern const char ram[];
extern const char rom_type[];
extern const char stm32_bootloader_mode[];
extern const char disabled[];
extern const char enabled[];
extern const char oscillator[];
extern const char * const port_names[];
extern const char * const cs_values[];
extern const uint32_t chip_size_from_type[NUM_CHIP_TYPES];

#endif // CONSTANTS_H
